go4retro/FlashPak/doc/FlashPak Label.bmp

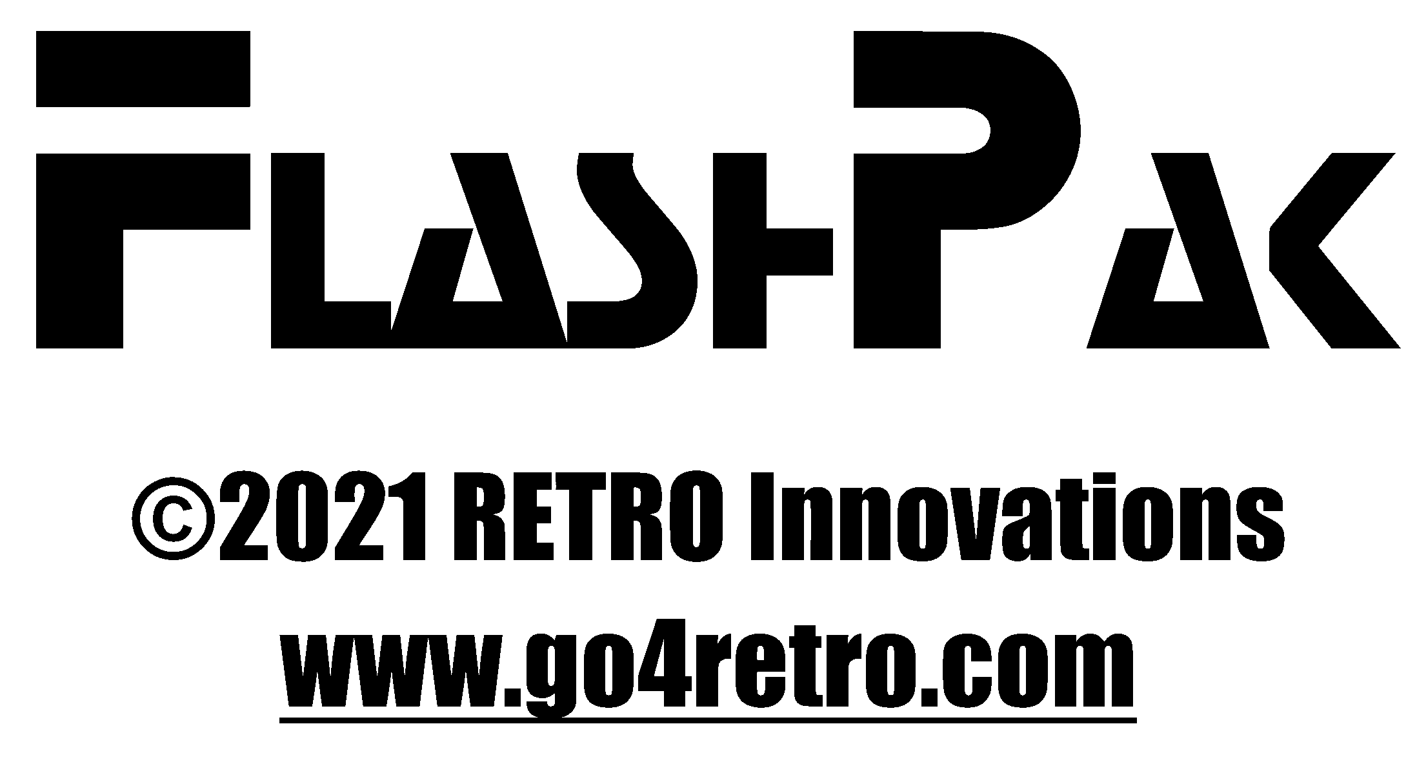
doc/FlashPak Label.bmp
